ppw0021/Arduino-Lasertag/lens render.png

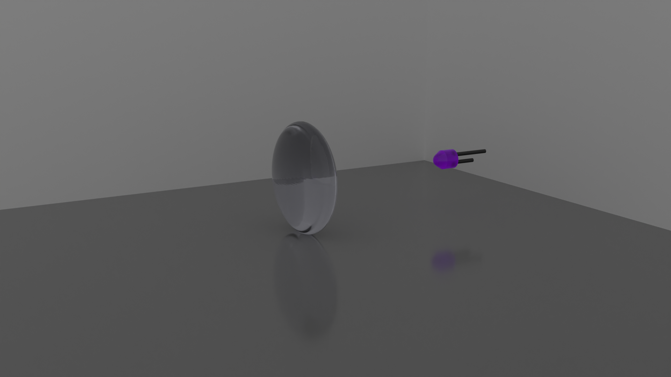
lens render.png
