ppw0021/Arduino-Lasertag/3D Models/Finished 3D Models/Black Parts/sights_round.stl

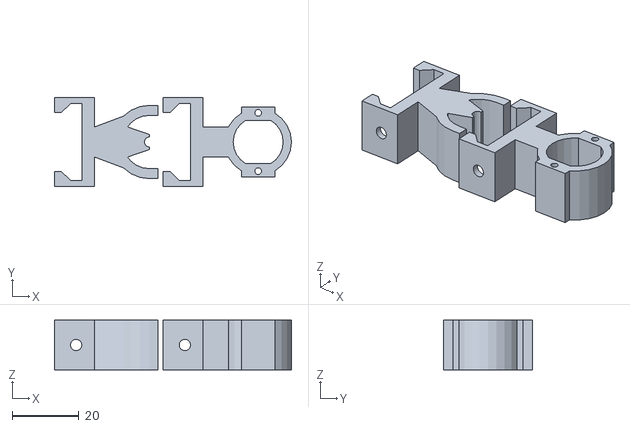
[picture p22: CAD file, 2024-01-03]
3D Models/Finished 3D Models/Black Parts/sights_round.stl
71.1 x 26.6 x 15.0
