ppw0021/Arduino-Lasertag/3D Models/Finished 3D Models/Black Parts/stock.stl

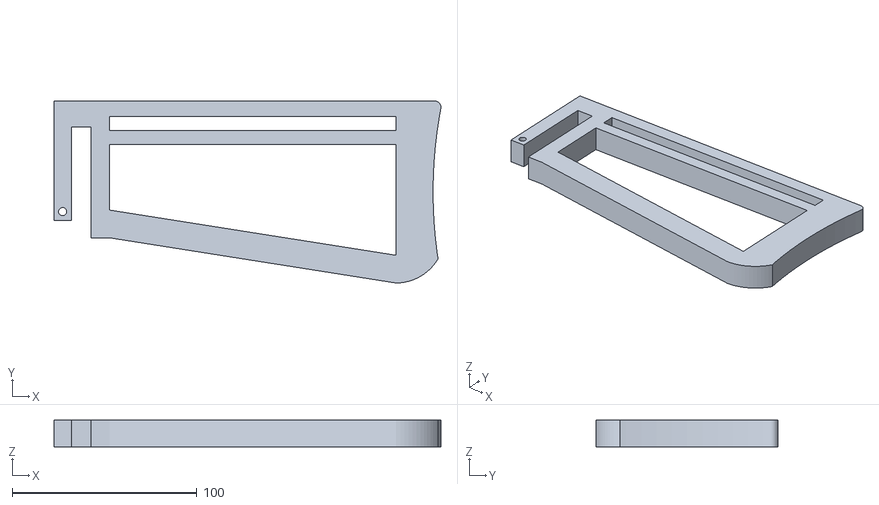
[picture p23: CAD file, 2024-01-03]
3D Models/Finished 3D Models/Black Parts/stock.stl
209.3 x 98.5 x 14.5
